Sirius-RX/SDVX-SP_Con/Software/Code/Debug.H

/********************************** (C) COPYRIGHT *******************************
* File Name          : Debug.H
* Author             : WCH
* Version            : V1.0
* Date               : 2020/07/03
* Description        : This file contains all the functions prototypes for UART
*                      Printf , Delay functions.									 
*******************************************************************************/
#ifndef	__DEBUG_H__
#define __DEBUG_H__

#include <absacc.h>
#include <stdio.h>
#include <string.h>
#include <intrins.h>
#include "CH557X.H"

//定义函数返回值
#ifndef  SUCCESS
#define  SUCCESS    0
#endif
#ifndef  FAIL
#define  FAIL       0xFF
#endif


#define	FREQ_SYS	                       48000000    //系统主频48MHz
#define  OSC_EN_XT                       0           //外部晶振使能，默认开启内部晶振
#ifndef  UART0_BUAD                                    
#define  UART0_BUAD                      115200        
#define  UART1_BUAD                      57600         
#endif                                                 
#ifndef  DE_PRINTF                                   //程序Pirntf输出开启
#define  DE_PRINTF                       0
#endif

#ifndef MIN
#define MIN(a,b)                (((a) <= (b)) ? (a) : (b))
#endif

void CfgFsys(void);                                  //CH557时钟选择和配置
void mDelayuS(UINT16 n);                             //以uS为单位延时
void mDelaymS(UINT16 n);                             //以mS为单位延时
void mInitSTDIO(void);                               //T1作为波特率发生器
  
#endif
